JeffRocchio/NixeTubesShieldNCS314/Case/20230125_Case-Mock-Up-Lit.jpg

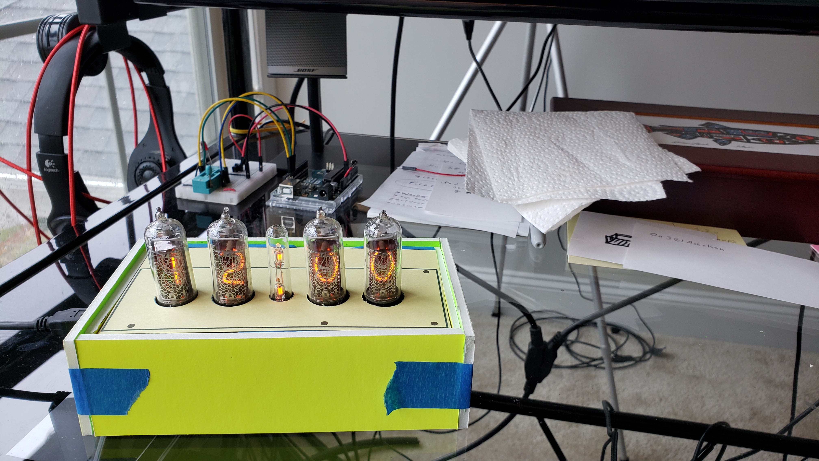
Case/20230125_Case-Mock-Up-Lit.jpg
