JeffRocchio/NixeTubesShieldNCS314/Case/20230125_Case-Mock-Up.jpg

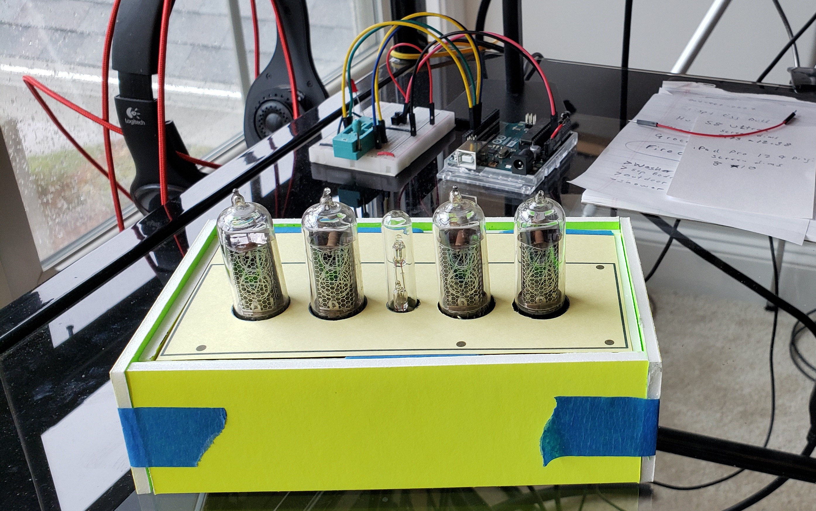
Case/20230125_Case-Mock-Up.jpg
