JeffRocchio/NixeTubesShieldNCS314/Case/Finished-Case-in-Use_01.jpg

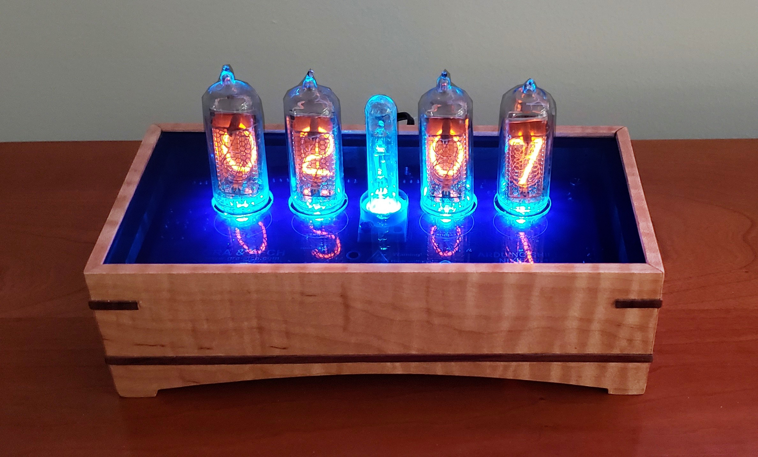
Case/Finished-Case-in-Use_01.jpg
