JeffRocchio/NixeTubesShieldNCS314/Case/Finished-Case-in-Use_02.jpg

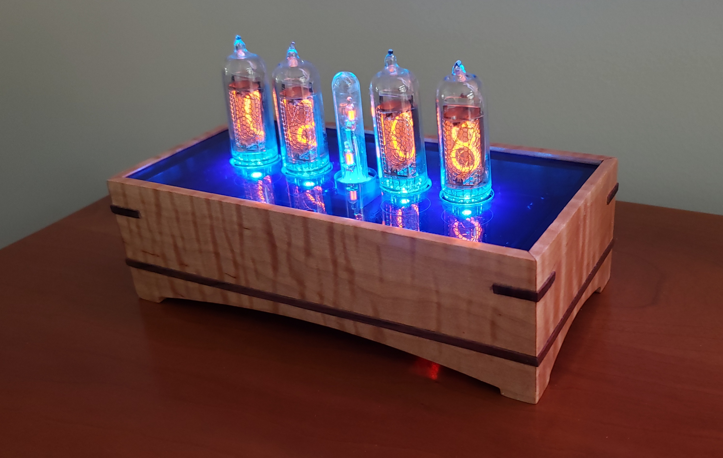
Case/Finished-Case-in-Use_02.jpg
