JeffRocchio/NixeTubesShieldNCS314/Case/Finished_Rear.jpg

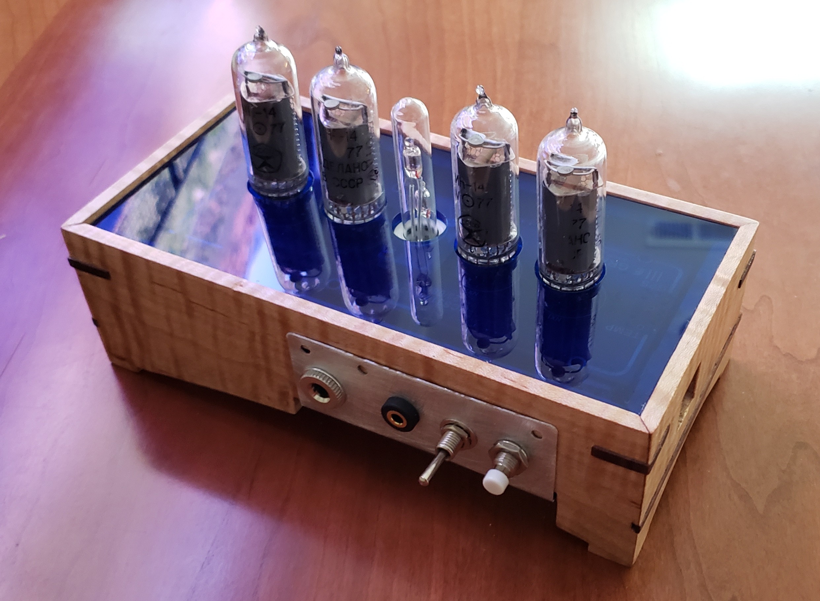
Case/Finished_Rear.jpg
