JeffRocchio/NixeTubesShieldNCS314/Case/Finished_USBside.jpg

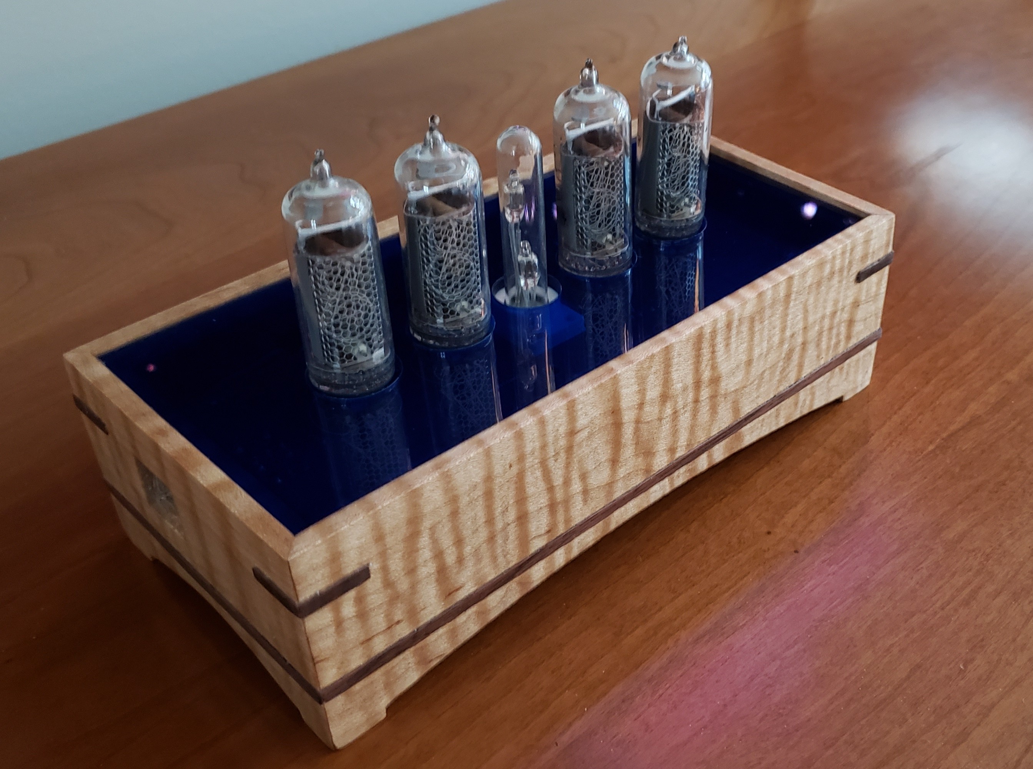
Case/Finished_USBside.jpg
