JeffRocchio/NixeTubesShieldNCS314/Case/Fabrication_Bottom-Plate_01.jpg

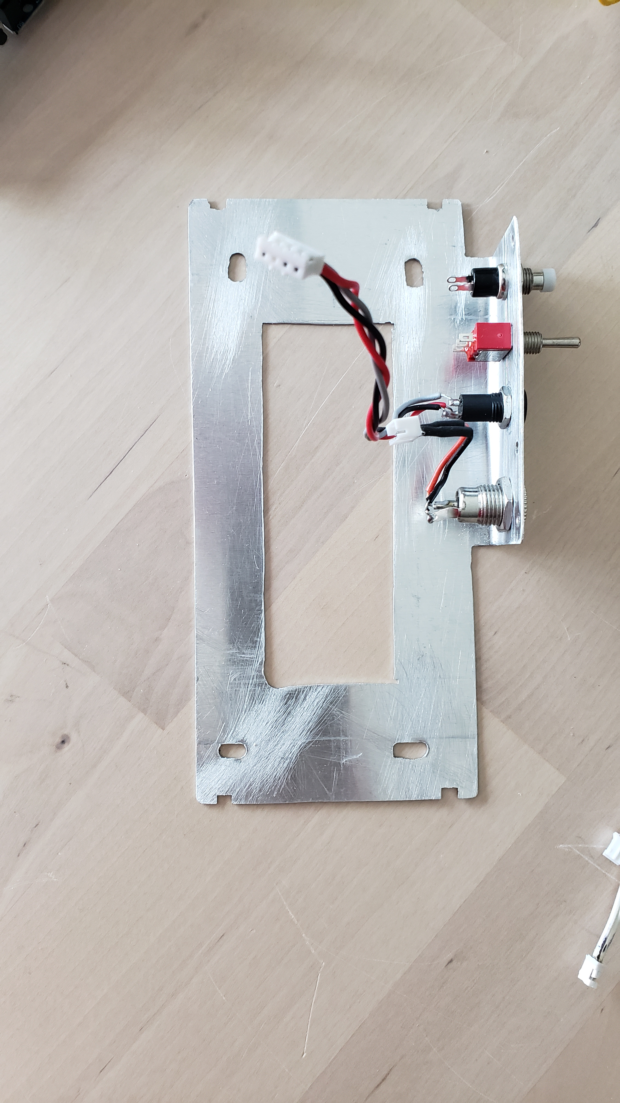
Case/Fabrication_Bottom-Plate_01.jpg
