JeffRocchio/NixeTubesShieldNCS314/Case/Fabrication_Ready4TopPlate_b.jpg

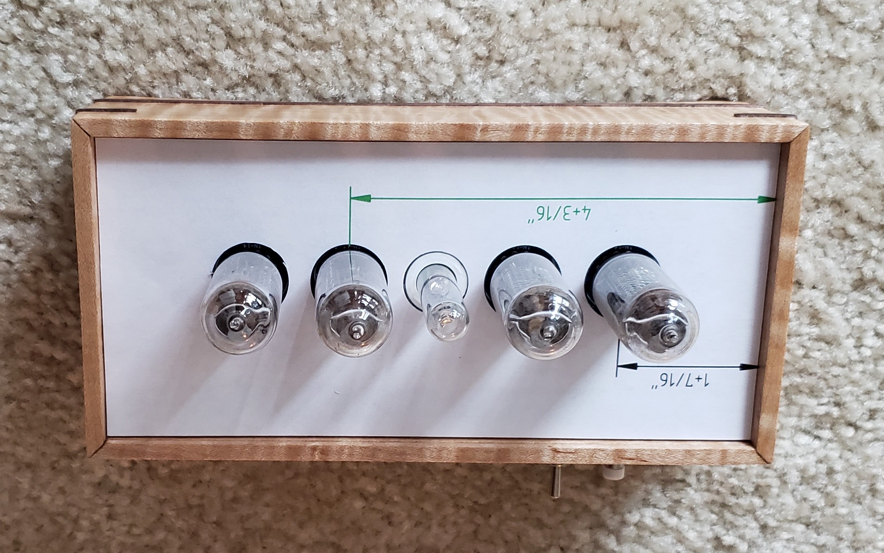
Case/Fabrication_Ready4TopPlate_b.jpg
