JeffRocchio/NixeTubesShieldNCS314/Case/Fabrication_Top-Plate.jpg

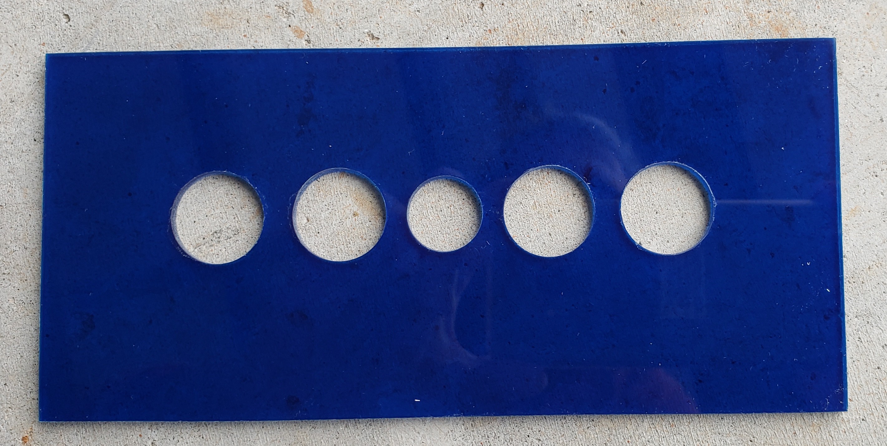
Case/Fabrication_Top-Plate.jpg
