JeffRocchio/NixeTubesShieldNCS314/Case/Fabrication_USBcutout.jpg

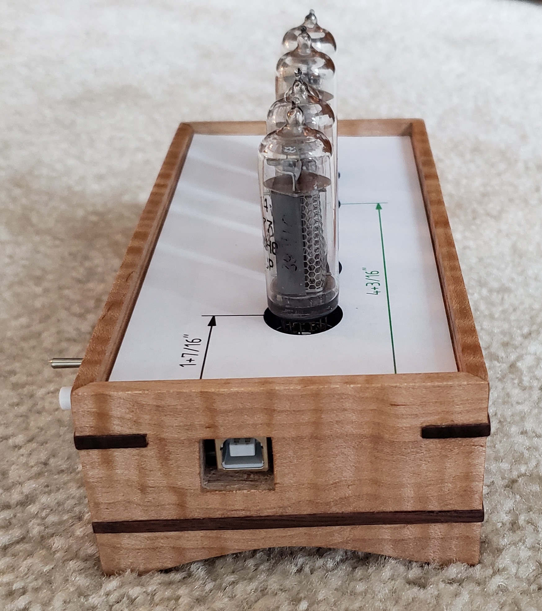
Case/Fabrication_USBcutout.jpg
